open-pages-org/thorzone-mjolnir-case/assets/Case_back.jpg

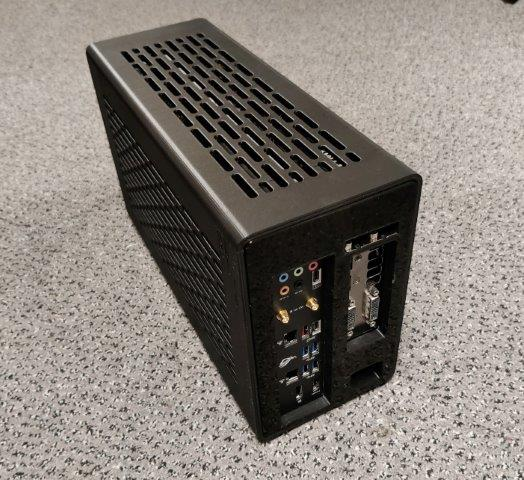
assets/Case_back.jpg
