open-pages-org/thorzone-mjolnir-case/assets/Case_front2.jpg

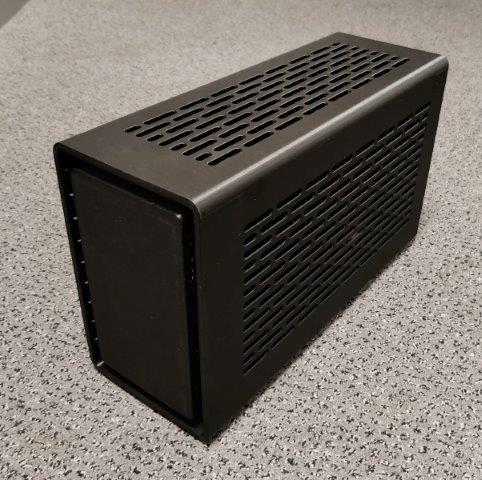
assets/Case_front2.jpg
