open-pages-org/thorzone-mjolnir-case/assets/PC_Case_retaining_screw_cover.JPG

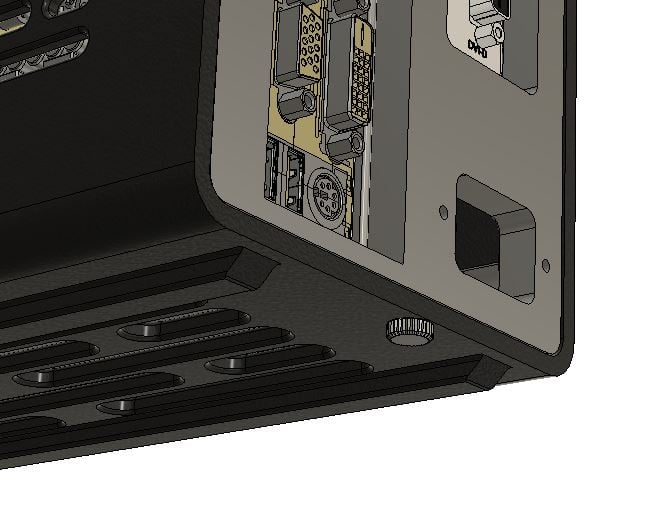
assets/PC_Case_retaining_screw_cover.JPG
