open-pages-org/thorzone-mjolnir-case/assets/SSD_and_Touch_Switch_location.JPG

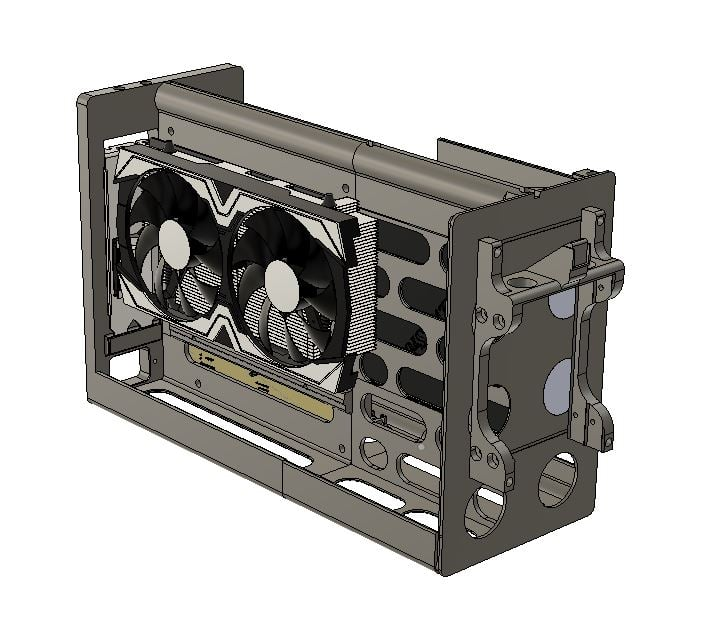
assets/SSD_and_Touch_Switch_location.JPG
